SunburyAdm/Road_Reflector/01-device-layer/hardware/Docs/Battery Selection.docx

Technical Analysis: Battery Selection for Smart Road Reflector Prototype for Ohio Road Conditions

1. Problem Definition

The smart road reflector project requires an energy storage solution capable of supporting an embedded sensing node installed in outdoor roadway conditions in Ohio. The device is expected to operate with low power consumption, solar charging, wireless communication, vibration/event sensing, and long-term exposure to cold winters, summer heat, snow, ice, water, salt, vibration, and freeze-thaw cycles.

The main technical problem is to identify the best battery option that balances:

- Energy capacity
- Cost per unit and cost per Wh
- Physical size and mechanical integration
- Cold-weather charging capability
- Thermal safety risk
- Required protection circuitry
- Solar charging compatibility
- Long-term reliability in roadway environments

The battery cannot be selected only by nominal capacity. For a road-mounted product, the correct selection must consider the full operating environment, especially low-temperature charging and high-temperature exposure inside the enclosure.

2. Application Context

The device is expected to work as a low-power smart road reflector or roadway sensor marker. The preliminary architecture includes:

- ESP32-C3 or similar low-power microcontroller
- LoRa wireless communication
- Accelerometer or vibration sensor
- Piezoelectric wake-up sensor
- NTC temperature sensing
- Small solar panel
- Rechargeable energy storage
- Outdoor sealed enclosure

The system is expected to spend most of its time in deep sleep and wake only when a vehicle, vibration event, or scheduled transmission occurs.

A representative operating strategy is:

Sleep mode

↓

Piezoelectric or accelerometer wake-up

↓

Short sensor acquisition window

↓

Local processing

↓

LoRa transmission

↓

Return to sleep

This architecture makes low average current possible, but the final battery choice still depends on real measured consumption.

3. Environmental Constraints for Ohio Road Deployment

For Ohio roadway conditions, the battery system must be designed for:

- Winter cold temperatures
- Snow and ice exposure
- Freeze-thaw cycles
- Road salt and moisture
- Summer pavement heating
- Solar exposure
- Enclosure heating above ambient temperature
- Mechanical shock and vibration
- Limited solar availability during winter

A practical preliminary design range should be:

Target ambient operating range:

-30 °C to +45 °C

Possible internal enclosure range:

-30 °C to +70 °C

Battery charging control:

Temperature-dependent and chemistry-specific

The most important constraint is cold-weather charging. Many lithium chemistries can discharge below 0 °C but should not be charged below 0 °C unless specifically rated for that condition. This is critical for a solar-powered road device because the panel may produce charge current during freezing conditions.

4. Battery Options Analyzed

This analysis compares three candidate options:

1. Nichicon SLB12400L1511CV
2. LiFePO₄ 32700
3. LiFePO₄ 18650

5. Option 1: SLB12400L1511CV

5.1 Description

The SLB12400L1511CV is a small rechargeable lithium titanate-type battery intended for IoT, energy harvesting, and long-cycle applications.

Approximate electrical characteristics:

Nominal voltage: 2.4 V

Nominal capacity: 150 mAh

Approximate energy: 2.4 V × 0.150 Ah = 0.36 Wh

Maximum charge voltage: 2.8 V

Minimum discharge voltage: 1.8 V

5.2 Advantages

The strongest advantage of the SLB12400L1511CV is environmental robustness. It is suitable for cold-region operation and has very high cycle life. This makes it technically attractive for a solar-powered device that may experience frequent shallow charge/discharge cycles.

Main advantages:

- Excellent cycle life
- Better cold-weather behavior than standard LiFePO₄
- Lower thermal safety risk
- Small physical size
- Good match for energy harvesting applications
- Suitable for very low-power IoT nodes
- Better fit for long-term maintenance-free operation

5.3 Disadvantages

The main limitation is energy capacity. At approximately 0.36 Wh, one SLB12400L1511CV stores far less energy than either LiFePO₄ option. This means the electronics must be extremely optimized.

Main disadvantages:

- Very limited energy storage
- Higher cost per Wh
- May require several cells in parallel for practical autonomy
- Requires charger design compatible with 2.8 V maximum charge voltage
- Not directly compatible with common single-cell LiFePO₄ charger ICs designed for 3.65 V termination

5.4 Technical Assessment

The SLB12400L1511CV is the best option from a cold-weather and cycle-life perspective, but it is not the best option for early prototypes because its low energy capacity leaves little margin for firmware inefficiency, frequent LoRa transmissions, sensor debugging, or low solar availability.

It is a strong candidate for a final ultra-low-power product only after the system energy budget is proven.

6. Option 2: LiFePO₄ 32700

6.1 Description

The LiFePO₄ 32700 is a larger cylindrical lithium iron phosphate cell. It provides significantly more energy than a 18650 LiFePO₄ cell while maintaining a safer chemistry than standard Li-ion NMC/NCA cells.

Approximate electrical characteristics:

Nominal voltage: 3.2 V

Typical capacity: 6000 mAh

Approximate energy: 3.2 V × 6.0 Ah = 19.2 Wh

Charge voltage: 3.65 V

6.2 Advantages

The LiFePO₄ 32700 provides the strongest energy reserve among the three options. This is valuable during winter, cloudy weather, higher event counts, firmware debugging, and field testing.

Main advantages:

- High energy capacity
- Good cost per Wh
- Safer than standard Li-ion
- Compatible with common LiFePO₄ charging architecture
- Large autonomy margin
- Good candidate for field prototypes
- Better tolerance for uncertain real-world consumption

6.3 Disadvantages

The key weakness is low-temperature charging. Standard LiFePO₄ cells generally should not be charged below 0 °C unless they are specifically rated for low-temperature charging. In Ohio, this requires active charge blocking during freezing conditions.

Main disadvantages:

- Larger size
- Higher weight
- Cannot be charged below 0 °C without special cell rating or heating strategy
- More stored energy means higher fault consequence than smaller cells
- Requires robust protection circuit and mechanical containment
- May be too large for compact reflector designs

6.4 Technical Assessment

The LiFePO₄ 32700 is the best practical option when the priority is energy, cost, and prototype reliability. It provides enough energy margin to support testing and field validation. However, for Ohio road deployment, it must include thermal charge protection.

The minimum required protection strategy is:

If battery temperature < 0 °C:

Disable solar charging

If battery temperature > 45–50 °C:

Disable or reduce charging

If battery temperature > 60 °C:

Enter thermal protection mode

If battery voltage is too low:

Disable non-critical loads

If battery voltage is too high:

Stop charging

7. Option 3: LiFePO₄ 18650

7.1 Description

The LiFePO₄ 18650 is a smaller cylindrical lithium iron phosphate cell. It has less energy than a 32700 but is easier to integrate mechanically.

Approximate electrical characteristics:

Nominal voltage: 3.2 V

Typical capacity: 1500 mAh

Approximate energy: 3.2 V × 1.5 Ah = 4.8 Wh

Charge voltage: 3.65 V

7.2 Advantages

The LiFePO₄ 18650 is a good balance for early prototypes. It is compact, widely available, relatively low cost, and easier to fit inside small enclosures.

Main advantages:

- Compact size
- Lower cost per cell
- Easier mechanical integration than 32700
- Safer than standard Li-ion
- Compatible with common LiFePO₄ chargers
- Good prototype battery
- Enough energy for early low-power testing

7.3 Disadvantages

The 18650 has much less energy than the 32700. This limits autonomy during winter, cloudy conditions, or high communication activity.

Main disadvantages:

- Lower energy reserve than 32700
- Same cold-charging limitation as other standard LiFePO₄ cells
- Less margin for firmware inefficiency
- May require larger solar panel or lower duty cycle
- Still requires thermal charge protection

7.4 Technical Assessment

The LiFePO₄ 18650 is the best first prototype option if the enclosure must remain compact. It is also useful for validating the power architecture before committing to a larger cell. However, if long field autonomy is required, the 32700 is more attractive.

8. Comparative Summary

Parameter | SLB12400L1511CV | LiFePO₄ 32700 | LiFePO₄ 18650
Nominal voltage | 2.4 V | 3.2 V | 3.2 V
Capacity | 150 mAh | ~6000 mAh | ~1500 mAh
Approx. energy | 0.36 Wh | 19.2 Wh | 4.8 Wh
Energy reserve | Very low | High | Medium
Size | Very small | Large | Medium
Cost per Wh | High | Low/medium | Low/medium
Cold operation | Excellent | Moderate | Moderate
Cold charging | Strong advantage | Needs blocking below 0 °C | Needs blocking below 0 °C
Thermal risk | Low | Medium | Medium-low
Solar compatibility | Good, but needs correct charger | Good with LiFePO₄ charger | Good with LiFePO₄ charger
Prototype margin | Low | High | Medium
Final product potential | High if ultra-low power | High if size allows | High for compact version

9. Main Engineering Trade-Off

The battery decision is a trade-off between environmental robustness and available energy.

The SLB12400L1511CV is technically attractive for long-life, cold-weather, low-risk operation, but it stores very little energy. It requires the complete system to be highly optimized.

The LiFePO₄ 32700 provides the best energy reserve and cost-per-energy balance, but it requires a larger enclosure and strict thermal charge control.

The LiFePO₄ 18650 is the best intermediate option. It is easier to integrate than the 32700 and provides much more energy than the SLB, but it still requires low-temperature charging protection.

10. Preliminary Recommendation

For the current project phase, the recommended path is:

Prototype Phase:

Use LiFePO₄ 18650 first.

Field Prototype / Extended Testing:

Move to LiFePO₄ 32700 if the enclosure allows the size.

Final Ultra-Low-Power Product:

Evaluate SLB12400L1511CV or a larger LTO-based solution after real power consumption is measured.

The LiFePO₄ 18650 is the most practical starting point because it provides a reasonable balance between cost, size, availability, and energy. The LiFePO₄ 32700 should be considered for field prototypes requiring longer autonomy. The SLB12400L1511CV should be treated as a premium long-life option, not as the first prototype battery.

11. Required Thermal Protection

For Ohio road deployment, thermal protection is not optional. The design should include:

- NTC thermistor physically mounted near the battery cell
- Solar charge inhibit below 0 °C for LiFePO₄
- Solar charge inhibit above 45–50 °C
- System shutdown or reduced operation above 60 °C
- Low-voltage cutoff
- Overvoltage protection
- Reverse polarity protection
- Short-circuit protection
- Current limiting or fuse/PTC protection
- Waterproof and corrosion-resistant enclosure
- Mechanical isolation from shock and vibration
- Battery venting or safe failure path depending on enclosure design

12. Prototype Development Steps

Step 1: Measure the Real Power Profile

Measure current consumption in all operating states:

Deep sleep current

Sensor wake-up current

Accelerometer sampling current

Piezo wake circuit current

ESP32 active current

LoRa transmit current

LoRa receive current

Temperature measurement current

Voltage monitoring current

Solar charger quiescent current

The result should be converted into an average daily energy requirement:

Daily energy = sleep energy + sensing energy + communication energy + losses

Step 2: Build a Battery Test Platform

Create a small test board that can support:

- LiFePO₄ 18650
- ~~LiFePO~~~~₄ 32700~~
- ~~SLB12400L1511CV~~
- Battery voltage measurement
- Battery temperature measurement
- Solar input measurement
- Charge enable/disable control
- Load switching
- Data logging

Step 3: Implement Thermal Charge Control

The firmware must include battery temperature logic.

Minimum LiFePO₄ logic:

If battery_temp < 0 °C:

Disable solar charging

If 0 °C <= battery_temp <= 45 °C:

Allow normal charging

If battery_temp > 45 °C:

Disable or reduce charging

If battery_temp > 60 °C:

Disable high-power functions

Step 4: Run Bench Tests

Bench testing should include:

- Full charge/discharge cycles
- Deep sleep duration test
- LoRa transmission energy test
- Sensor event energy test
- Solar charging test
- Charger quiescent current test
- Low-voltage cutoff validation
- Cold battery discharge test
- Hot enclosure simulation

Step 5: Run Environmental Tests

Initial environmental tests should include:

Cold test: -20 °C to -30 °C

Hot test: +60 °C to +70 °C internal enclosure simulation

Thermal cycling: cold/hot repeated cycles

Humidity exposure

Water ingress check

Salt exposure consideration

Vibration test

Solar charging behavior test

Step 6: Field Test in Ohio Conditions

Install a limited number of prototypes in controlled test locations and log:

- Battery voltage
- Battery temperature
- Internal enclosure temperature
- Solar input voltage/current
- Number of wake-up events
- Number of LoRa transmissions
- Daily state of charge estimate
- Communication reliability
- False vibration detections
- Cold morning behavior
- Hot afternoon behavior

13. Project-Level Next Steps

13.1 Define Product Requirements

Before final battery selection, define:

Required autonomy without sun

Maximum allowed enclosure size

Target product cost

Expected number of events per day

Expected LoRa messages per day

Expected service life

Minimum winter operating temperature

Maximum internal summer temperature

Required installation method

Maintenance interval

13.2 Build Three Battery Variants

Create three prototype variants:

Variant A: LiFePO₄ 18650

Variant B: LiFePO₄ 32700

Variant C: SLB12400L1511CV or multiple SLB cells in parallel

Each variant should use the same sensor and communication firmware so the battery performance comparison is fair.

13.3 Select the Final Architecture Based on Measured Data

Final selection should be based on measured values, not assumptions.

Decision rules:

If average current is higher than expected:

Prefer LiFePO₄ 32700

If enclosure size is limited:

Prefer LiFePO₄ 18650

If the system becomes ultra-low-power and long service life is the priority:

Reconsider SLB / LTO

If winter charging is a hard requirement:

Prefer SLB / LTO or add battery heating / charge blocking strategy

13.4 Perform Safety and Reliability Review

Before productization, perform:

- Battery safety review
- Thermal risk analysis
- Failure Mode and Effects Analysis
- Charging circuit validation
- Enclosure sealing validation
- Connector corrosion review
- Mechanical shock review
- Solar charging reliability test
- Long-term outdoor exposure test

14. Conclusion

The best battery option depends on the maturity of the power design.

For the current stage, the LiFePO₄ 18650 is the recommended starting point because it is compact, affordable, safe, and provides enough energy for early validation.

For a more advanced field prototype, the LiFePO₄ 32700 is the strongest candidate because it provides much higher energy capacity and better autonomy margin, especially during winter and low-solar periods.

For a final highly optimized product, the SLB12400L1511CV or a larger LTO-based solution should be evaluated because it offers better cold-weather behavior, very high cycle life, and lower thermal risk. However, the SLB option is only practical if the electronics achieve extremely low average power consumption or if multiple cells are used in parallel.

Preliminary recommendation:

Prototype: LiFePO₄ 18650

Extended field prototype: LiFePO₄ 32700

Final premium low-maintenance design: SLB / LTO after power optimization

The immediate next step is to measure the real current consumption of the complete system and use that data to calculate required battery capacity for Ohio road conditions.
