SunburyAdm/Road_Reflector/01-device-layer/hardware/README.md

# Hardware

Hardware design files, recommended component stack, and bring-up notes for the
Smart Road Reflector node.

- `recomended-stack.txt` — recommended end-to-end component & software stack
- `commands.txt` — useful bring-up / tooling commands

See [`../README.md`](../README.md) for the core hardware target.
